Wout-M/QMK-ADB-to-USB/firmware/config.h

/*
Copyright 2011 Jun Wako <wakojun@gmail.com>

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
Ported to QMK by Peter Roe <pete@13bit.me>
*/

#pragma once

/* matrix size */
#define MATRIX_ROWS 16  // keycode bit: 3-0
#define MATRIX_COLS 8   // keycode bit: 6-4

/* Mechanical locking support. Use KC_LCAP, KC_LNUM or KC_LSCR instead in keymap */
#define LOCKING_SUPPORT_ENABLE
/* Locking resynchronize hack */
#define LOCKING_RESYNC_ENABLE

/* ADB port setting */
#define ADB_PORT        PORTD
#define ADB_PIN         PIND
#define ADB_DDR         DDRD
#define ADB_DATA_BIT    2
//#define ADB_PSW_BIT     1       // optional

#define OLED_TIMEOUT 0
